AiwendilsCode/Arduino-speech-commands-recognition/images_and_videos/image2.jpg

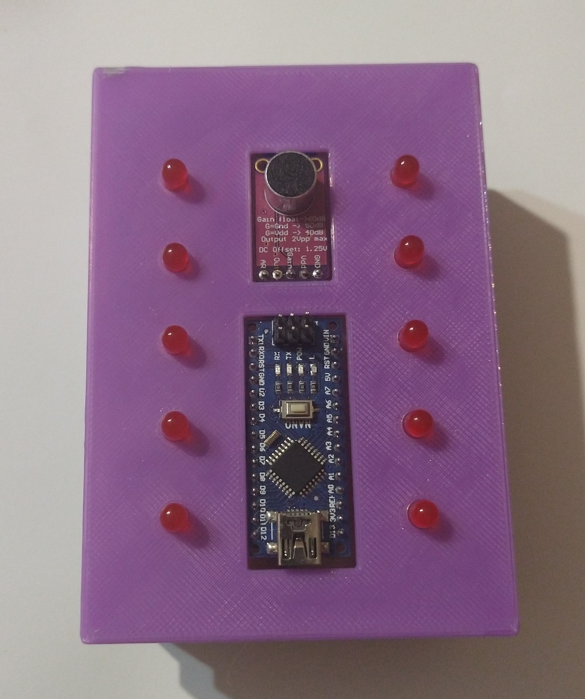
images_and_videos/image2.jpg
