AiwendilsCode/Arduino-speech-commands-recognition/images_and_videos/image3.jpg

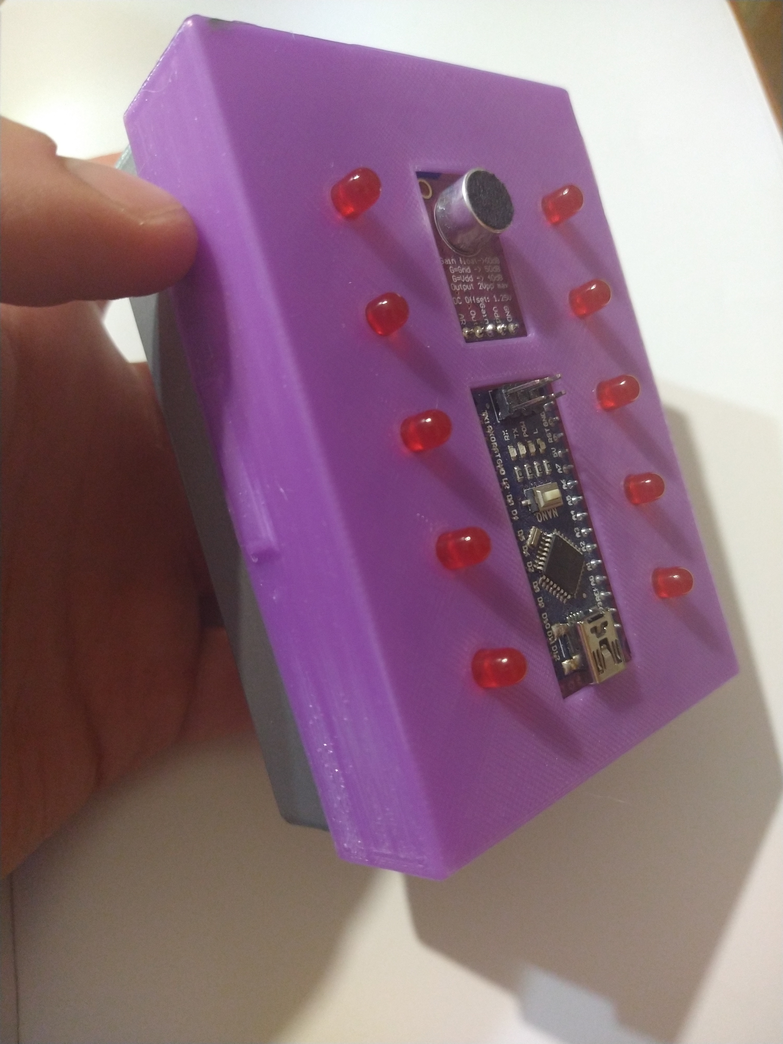
images_and_videos/image3.jpg
